hznwn/hn-axon-cell-neuromorphic-classifier/data/generated_classification_figures/accuracy_by_class.png

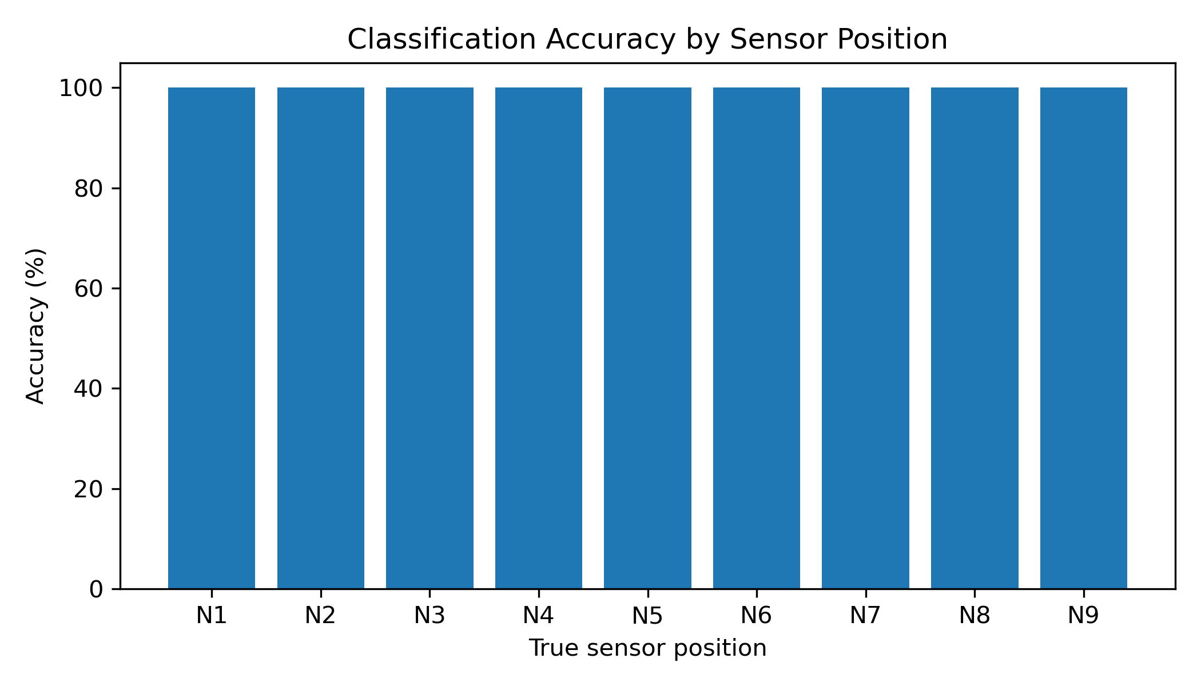
data/generated_classification_figures/accuracy_by_class.png
