hznwn/hn-axon-cell-neuromorphic-classifier/data/generated_classification_figures/classification_stability_over_time.png

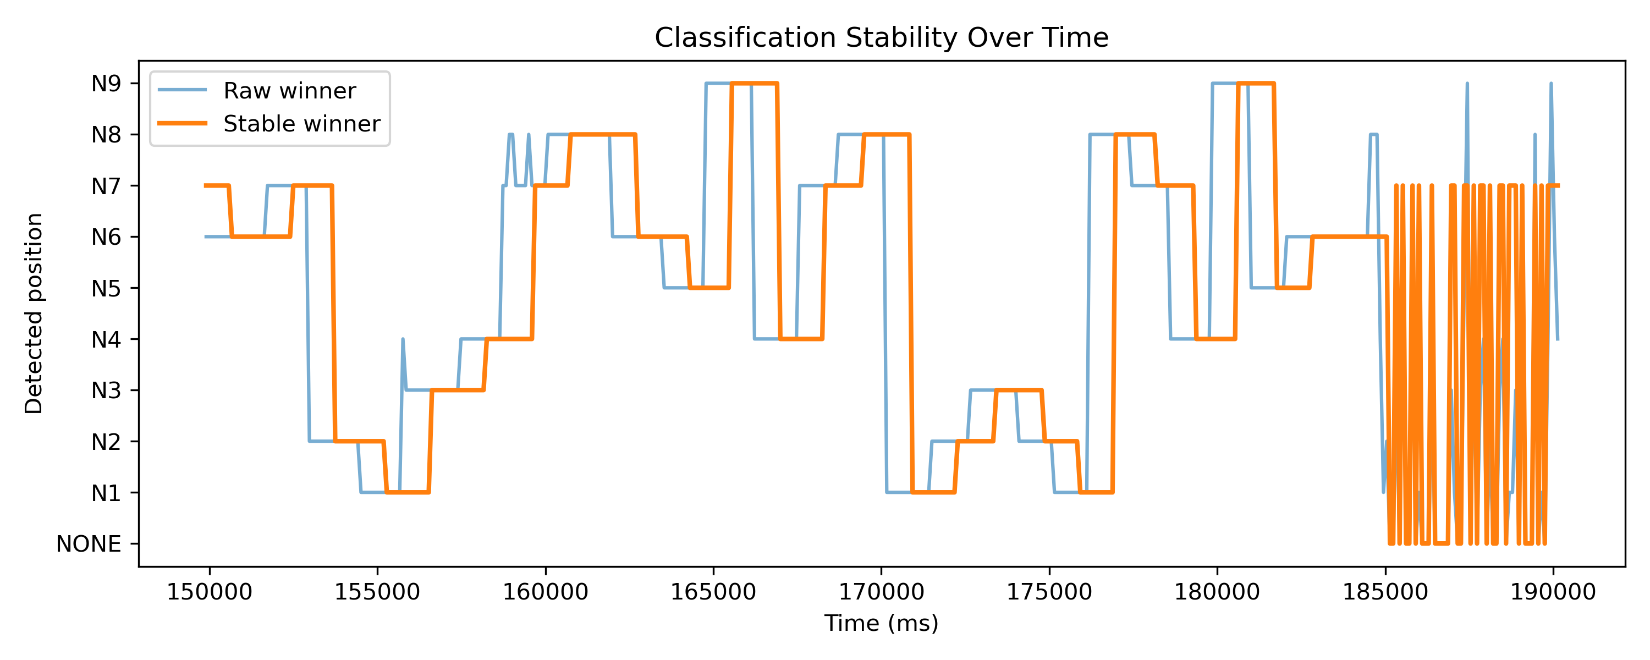
data/generated_classification_figures/classification_stability_over_time.png
