hznwn/hn-axon-cell-neuromorphic-classifier/data/generated_classification_figures/confusion_matrix_true_vs_predicted.png

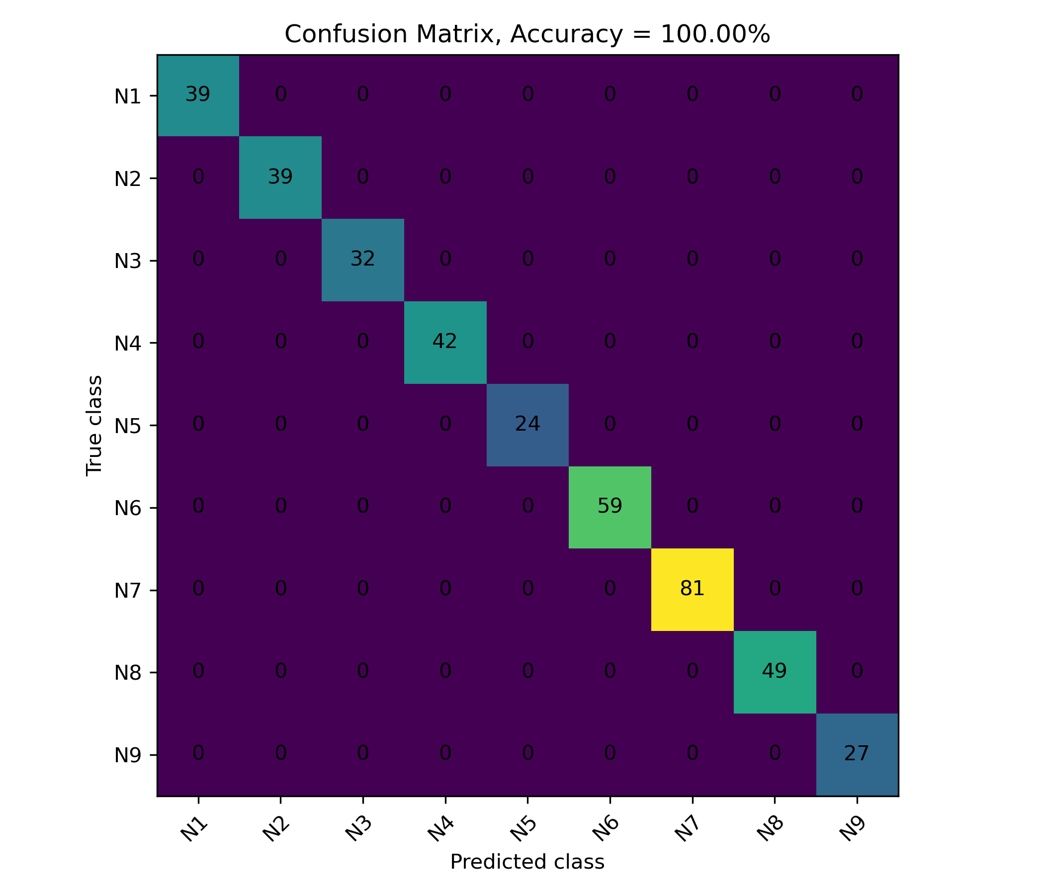
data/generated_classification_figures/confusion_matrix_true_vs_predicted.png
