hznwn/hn-axon-cell-neuromorphic-classifier/data/generated_classification_figures/per_class_sample_counts.png

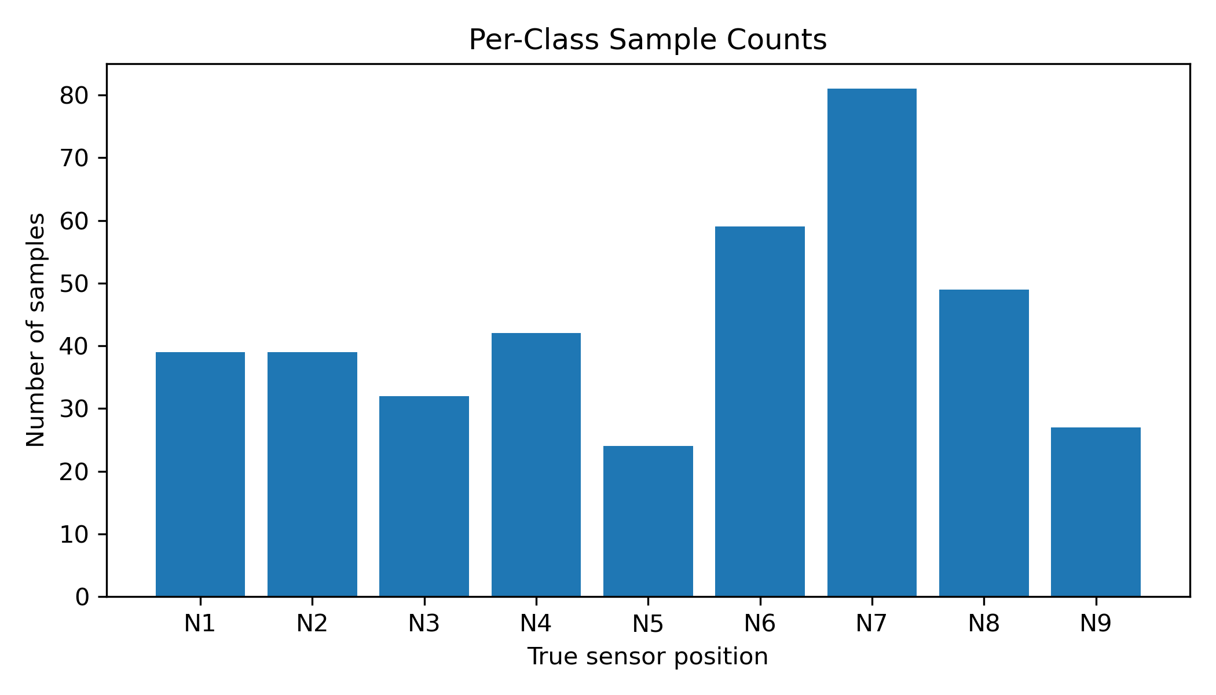
data/generated_classification_figures/per_class_sample_counts.png
