hznwn/hn-axon-cell-neuromorphic-classifier/data/generated_classification_figures/similarity_score_distribution.png

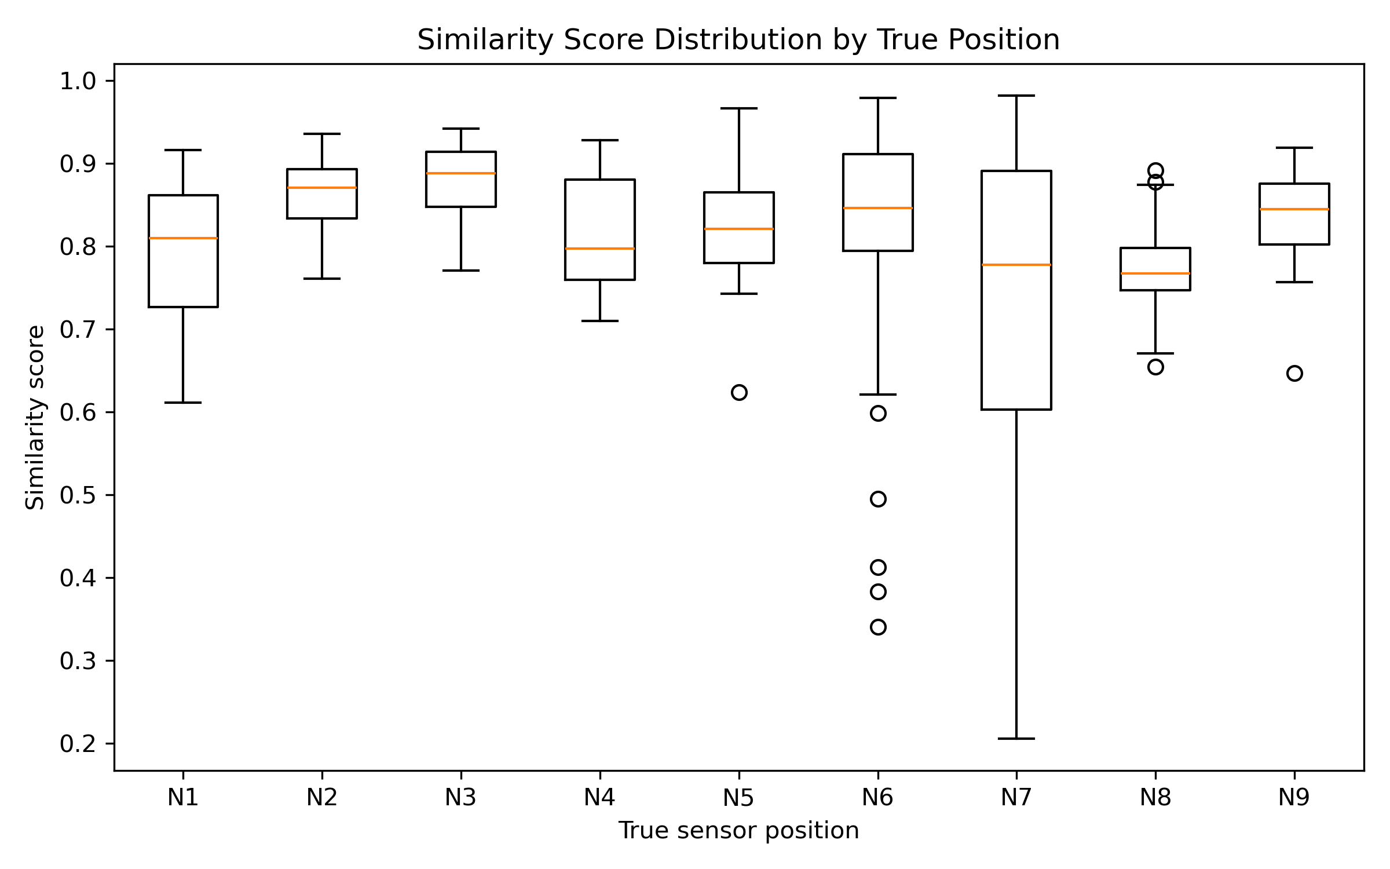
data/generated_classification_figures/similarity_score_distribution.png
